lencshu/IOT_meteo/3.Boitier/3Dprinting.jpg

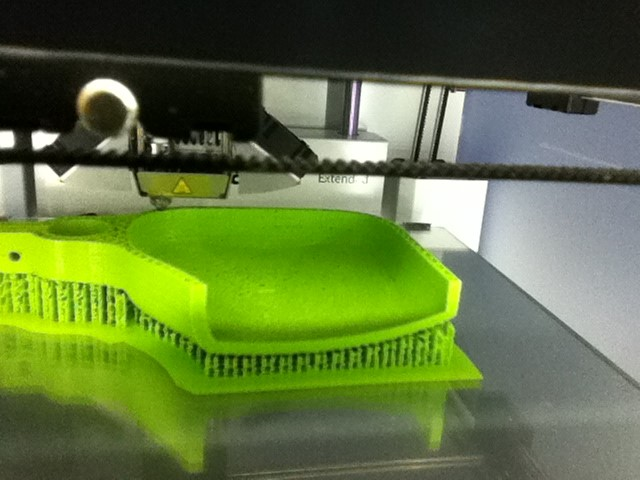
3.Boitier/3Dprinting.jpg
