lencshu/IOT_meteo/2.Web/WebView.png

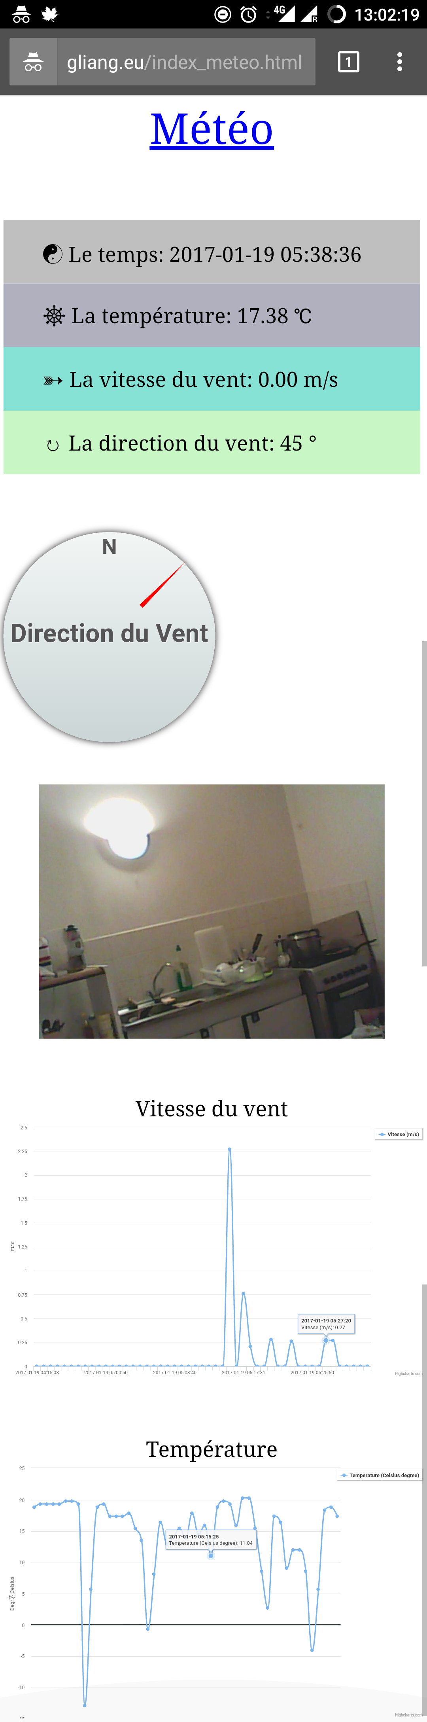
2.Web/WebView.png
