lencshu/IOT_meteo/2.Web/With PHP 5/meteoimage/meteo.png

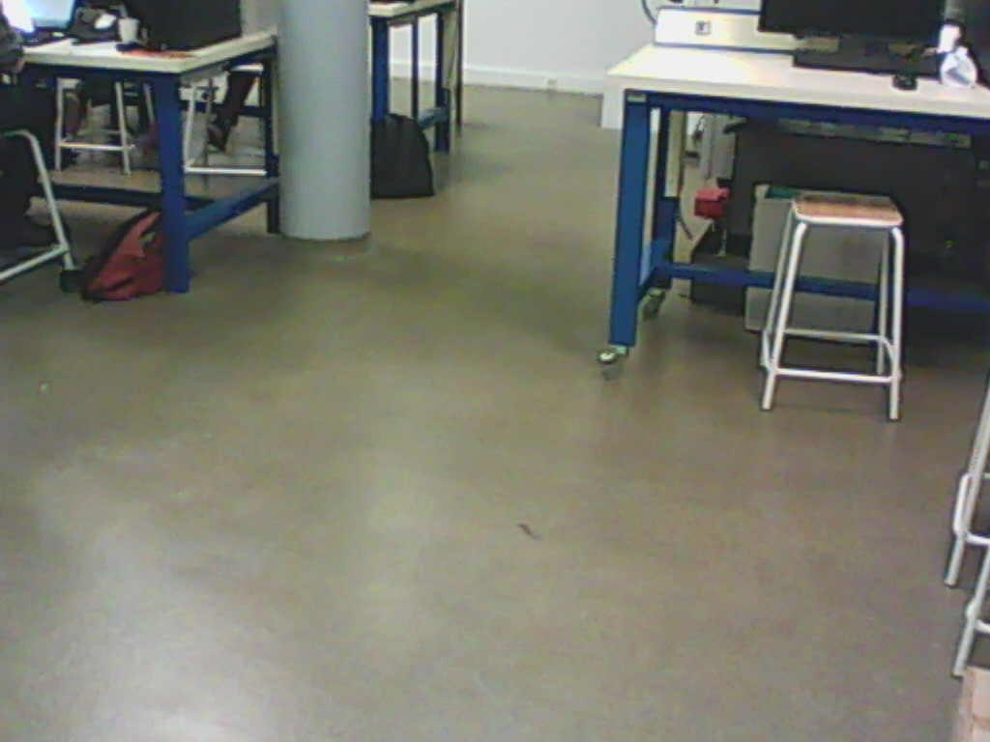
2.Web/With PHP 5/meteoimage/meteo.png
