lencshu/IOT_meteo/MultiMedia/cap_20171212_145410.png

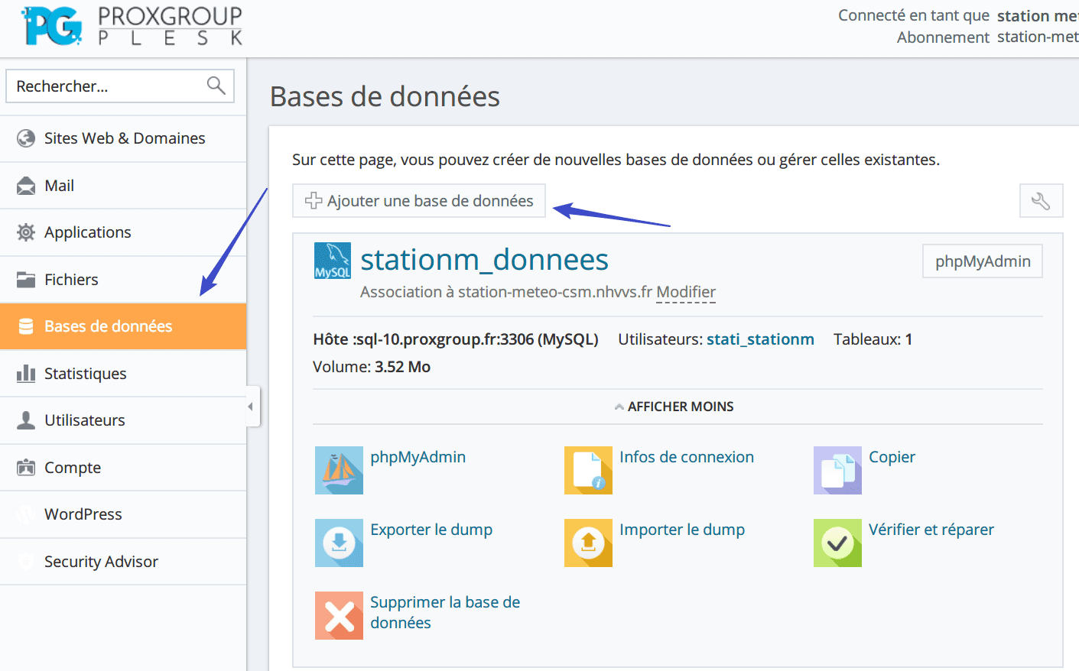
MultiMedia/cap_20171212_145410.png
