lencshu/IOT_meteo/MultiMedia/cap_20171212_145604.png

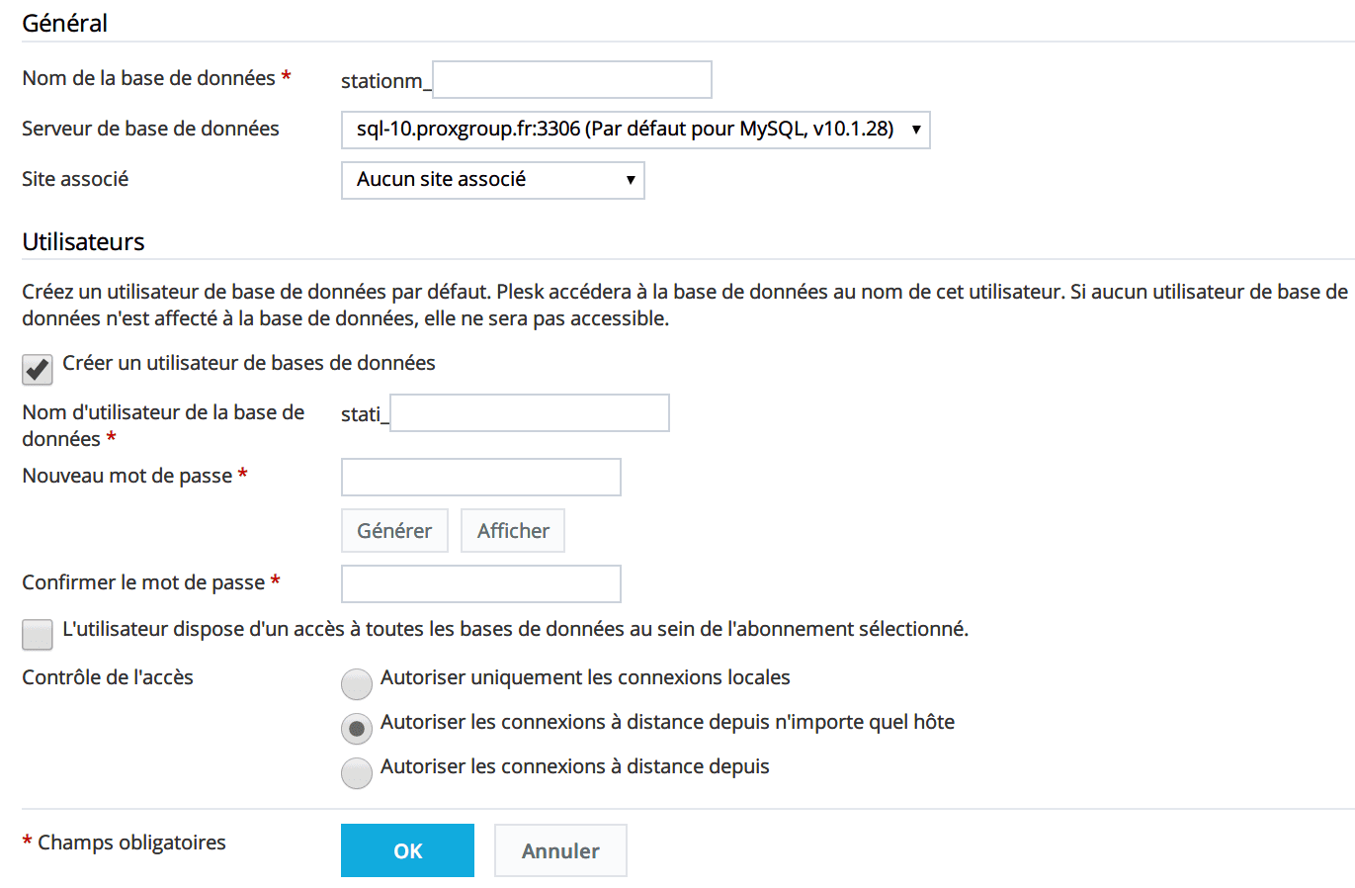
MultiMedia/cap_20171212_145604.png
