lencshu/IOT_meteo/MultiMedia/cap_20171212_150654.png

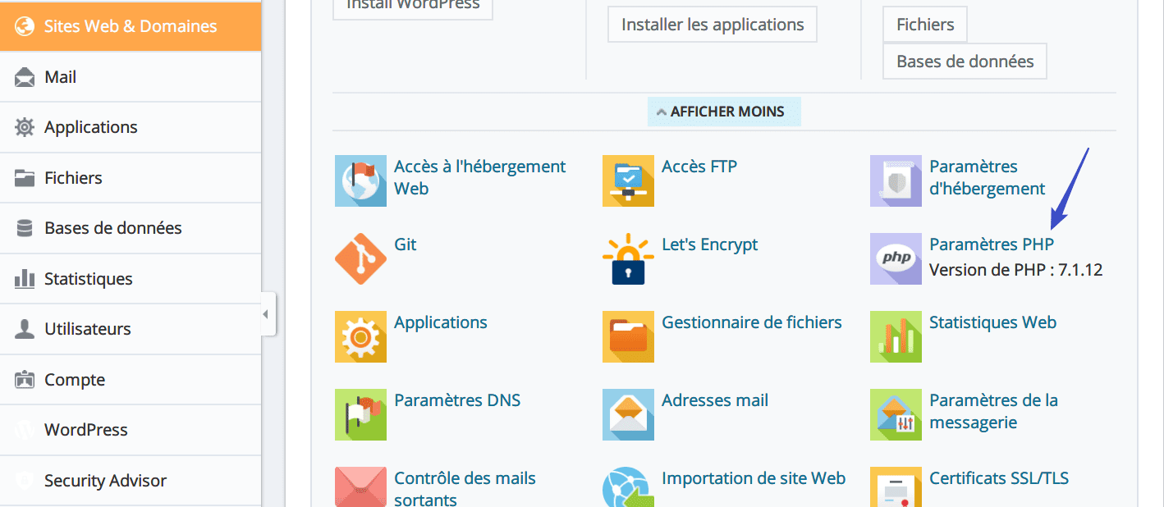
MultiMedia/cap_20171212_150654.png
