lencshu/IOT_meteo/MultiMedia/cap_20171212_150714.png

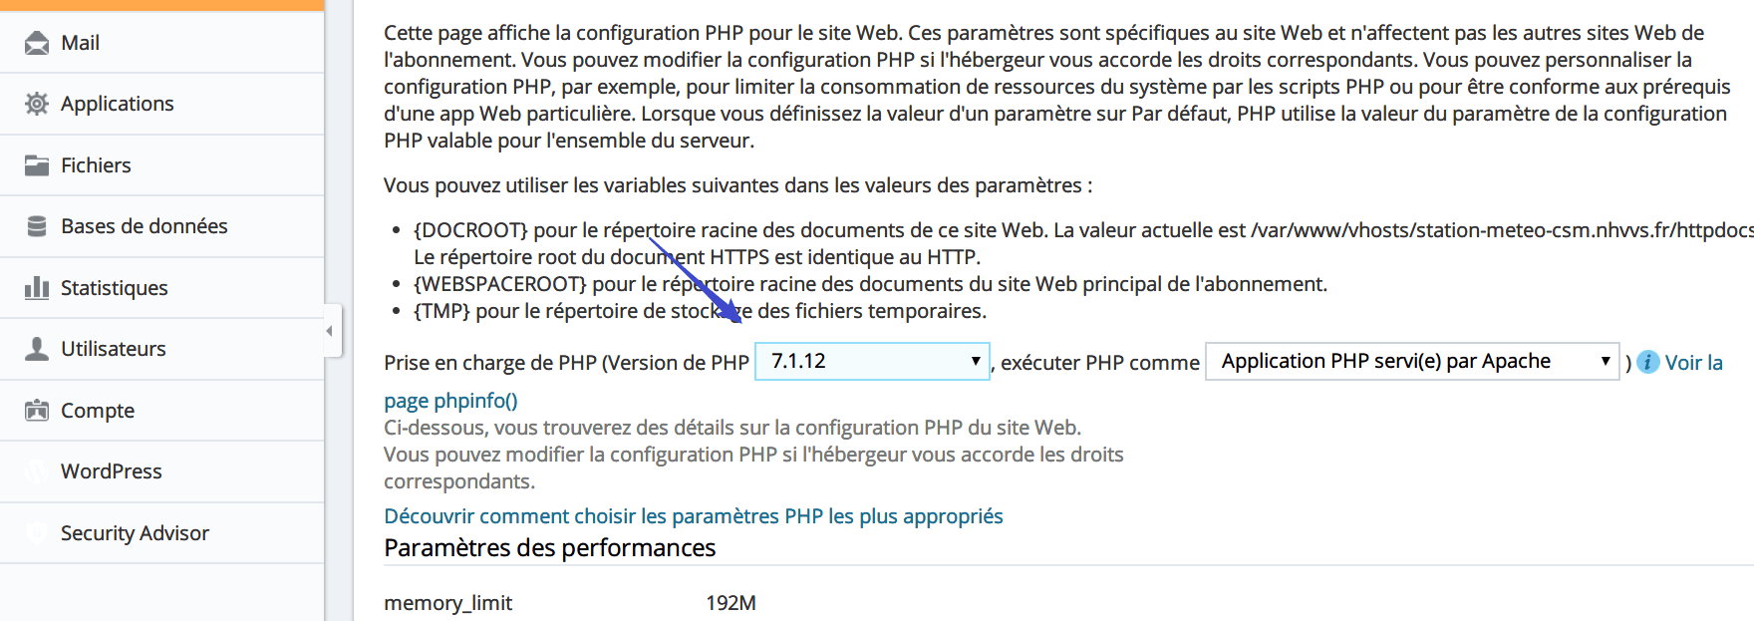
MultiMedia/cap_20171212_150714.png
