lencshu/IOT_meteo/MultiMedia/cap_20171212_154901.png

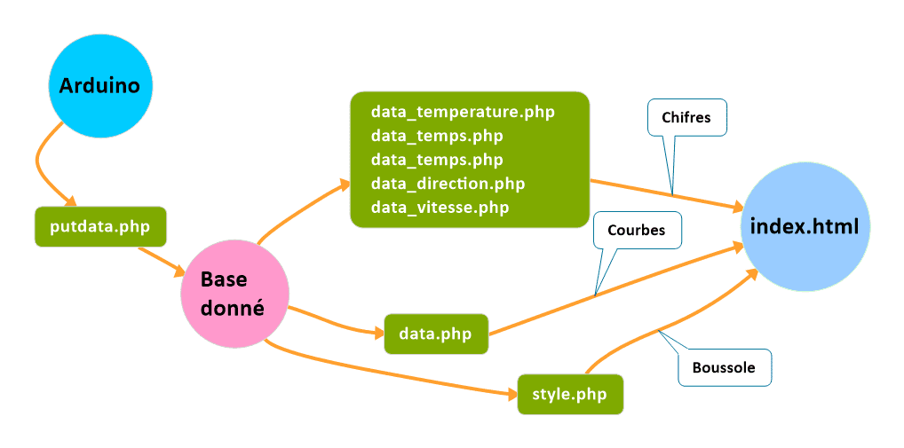
MultiMedia/cap_20171212_154901.png
