lencshu/IOT_meteo/MultiMedia/cap_20171212_155318.png

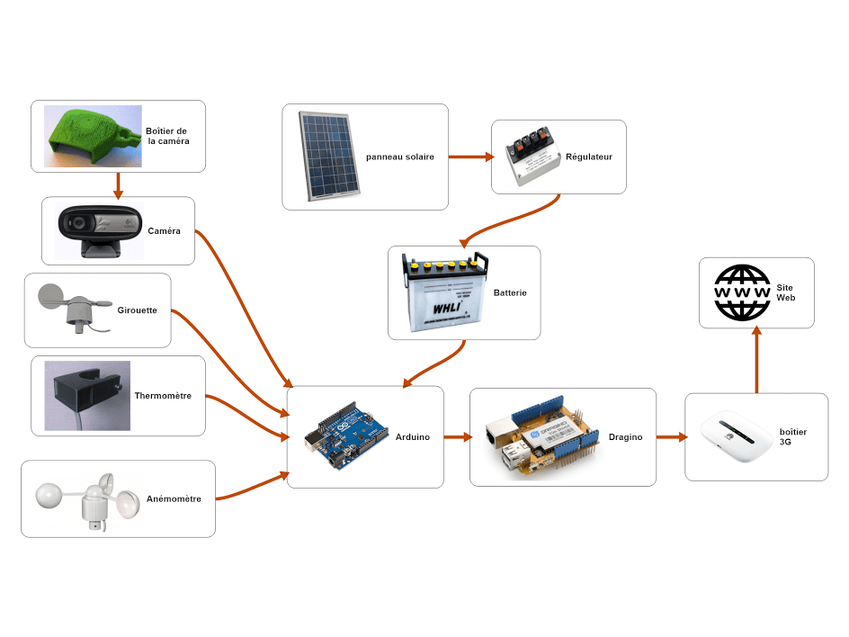
MultiMedia/cap_20171212_155318.png
