lencshu/IOT_meteo/MultiMedia/cap_20171212_213727.png

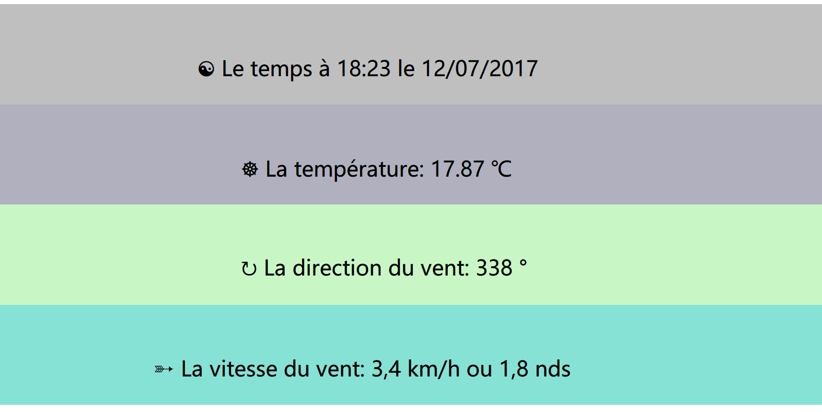
MultiMedia/cap_20171212_213727.png
