lencshu/IOT_meteo/MultiMedia/cap_20171212_214824.png

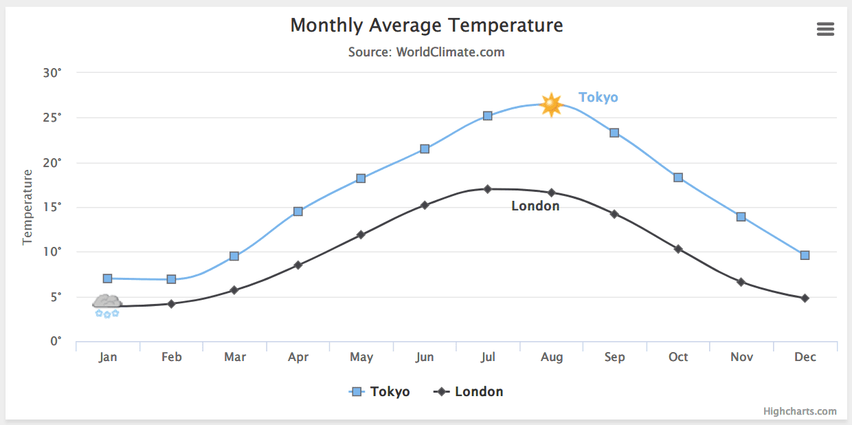
MultiMedia/cap_20171212_214824.png
