lencshu/IOT_meteo/MultiMedia/p1.png

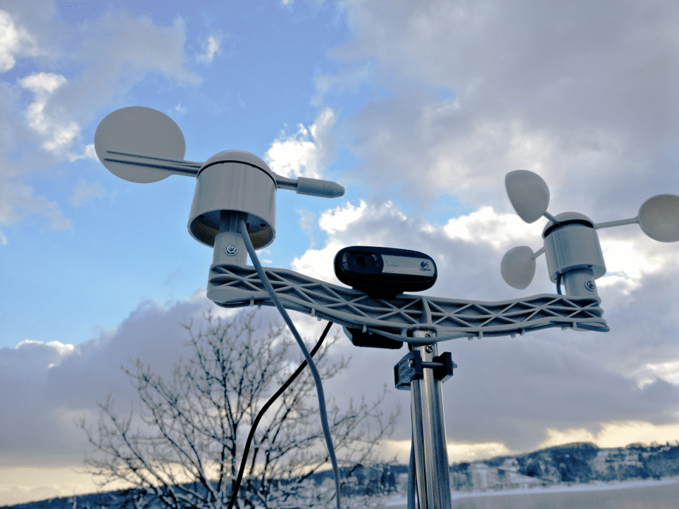
MultiMedia/p1.png
