lencshu/IOT_meteo/MultiMedia/p2.png

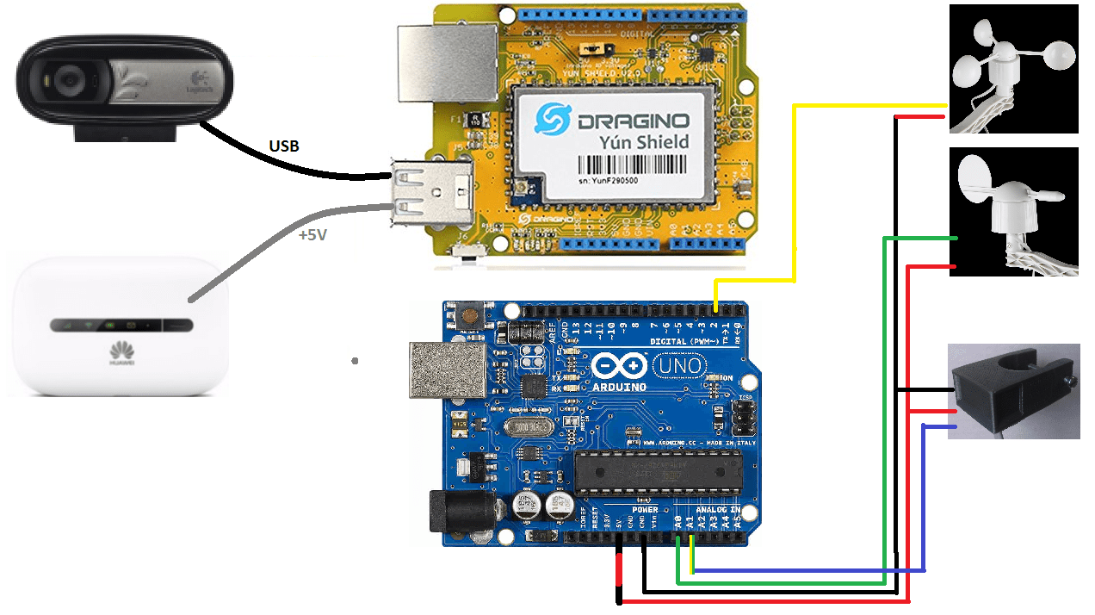
MultiMedia/p2.png
